markus1203/MoBiMet/Sensor_Test/Temperatur_and_Humidity/Data/FRWRTM_MET_1min_2020-04-05.csv

TOA5 | FRWRTM | CR1000X | 2600 | CR1000X.Std.03.02 | CPU:FRWRTM007.CR1X | 29908 | MET_1min
TIMESTAMP | RECORD | MET_PTB100_PressureSeaLevel_hPa_Avg | MET_PTB100_PressureActual_hPa_Avg | MET_CS215_AirTemperature_degC_Avg | MET_CS215_RelHumidity_percent_Avg | MET_CS215_DewPoint_degC_Avg | MET_CS215_VapourPressure_hPa_Avg | MET_CS215_VapPressDeficit_hPa_Avg | MET_CS215_MixingRatio_gKg_Avg | MET_CS107_SoilT05cm_degC_Avg | MET_CS107_SoilT20cm_degC_Avg
TS | RN | hPa | hPa | degC | % | degC | hPa | hPa | g/kg | degC | degC
 |  | Avg | Avg | Avg | Avg | Avg | Avg | Avg | Avg | Avg | Avg
2020-04-05 00:01:00 | 63954 | 1020.404 | 987.741 | 9.369334 | 53.05983 | 0.2502696 | 6.21867 | 5.50144 | 3.941242 | 10.80572 | 9.838089
2020-04-05 00:02:00 | 63955 | 1020.394 | 987.7316 | 9.36775 | 53.25433 | 0.2997386 | 6.240806 | 5.478066 | 3.955398 | 10.80352 | 9.836883
2020-04-05 00:03:00 | 63956 | 1020.37 | 987.7077 | 9.364333 | 52.95258 | 0.2174377 | 6.204032 | 5.512173 | 3.932038 | 10.80069 | 9.835658
2020-04-05 00:04:00 | 63957 | 1020.412 | 987.7499 | 9.370166 | 53.09183 | 0.2594223 | 6.222764 | 5.497997 | 3.943816 | 10.79503 | 9.833943
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
