markus1203/MoBiMet/Sensor_Test/Temperatur_and_Humidity/Data/FRWRTM_MET_1min_2020-04-06.csv

TOA5 | FRWRTM | CR1000X | 2600 | CR1000X.Std.03.02 | CPU:FRWRTM007.CR1X | 29908 | MET_1min
TIMESTAMP | RECORD | MET_PTB100_PressureSeaLevel_hPa_Avg | MET_PTB100_PressureActual_hPa_Avg | MET_CS215_AirTemperature_degC_Avg | MET_CS215_RelHumidity_percent_Avg | MET_CS215_DewPoint_degC_Avg | MET_CS215_VapourPressure_hPa_Avg | MET_CS215_VapPressDeficit_hPa_Avg | MET_CS215_MixingRatio_gKg_Avg | MET_CS107_SoilT05cm_degC_Avg | MET_CS107_SoilT20cm_degC_Avg
TS | RN | hPa | hPa | degC | % | degC | hPa | hPa | g/kg | degC | degC
 |  | Avg | Avg | Avg | Avg | Avg | Avg | Avg | Avg | Avg | Avg
2020-04-06 00:01:00 | 65394 | 1018.074 | 985.4112 | 9.117416 | 58.85733 | 1.465246 | 6.78321 | 4.741622 | 4.311748 | 11.76102 | 10.5164
2020-04-06 00:02:00 | 65395 | 1018.096 | 985.4339 | 9.11825 | 58.76458 | 1.443873 | 6.772895 | 4.752576 | 4.305046 | 11.75841 | 10.51471
2020-04-06 00:03:00 | 65396 | 1018.113 | 985.4507 | 9.124334 | 58.79433 | 1.456703 | 6.779078 | 4.751076 | 4.308928 | 11.75586 | 10.513
2020-04-06 00:04:00 | 65397 | 1018.112 | 985.4499 | 9.109 | 58.6995 | 1.419632 | 6.761217 | 4.757137 | 4.297502 | 11.75011 | 10.5115
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
