markus1203/MoBiMet/Sensor_Test/Temperatur_and_Humidity/Data/Ta_RH_Test-2020-04-03.csv

Time | AM2320_Ta | AM2320RH | 1_DHT22_Ta | 1_DHT22_RH | 2_DHT22_Ta | 2_DHT22_RH | 1_HTU21D_Ta | 1_HTU21D_RH | 2_HTU21D_Ta | 2_HTU21D_RH | 1_MCP9808 | 2_MCP9808 | 1_BME680_Ta | 1_BME680_RH | 1_BME680_P | 1_BME680_q | 2_BME680_Ta | 2_BME680_RH | 2_BME680_P | 2_BME680_q | 1_BME280_Ta | 1_BME280_RH | 1_BME280_P | 2_BME280_Ta | 2_BME280_RH | 2_BME280_P
2020-04-03 18:05:14 | 18.3 | 37.6 | 18.3999996185 | 28.8999996185 | 17.0 | 32.5 | 15.9990722656 | 32.1240844727 | 15.8167456055 | 32.4521484375 | 16.0625 | 16.3125 | 15.68 | 33.458 | 985.93 | 12887828 | 15.68 | 32.879 | 987.38 | 12917167 | 15.48 | 29.2887808946 | 985.581536506 | 15.24 | 15.24 | 986.07101426
2020-04-03 18:06:02 | 16.2 | 38.1 | 16.1000003815 | 31.8999996185 | 16.7999992371 | 31.8999996185 | 15.3341162109 | 35.5725708008 | 15.1839648437 | 35.6641235352 | 15.5625 | 15.875 | 15.23 | 34.886 | 985.95 | 12887828 | 15.17 | 34.578 | 987.36 | 12917167 | 15.04 | 31.5297082701 | 985.635545612 | 14.71 | 14.71 | 986.122666853
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
