markus1203/MoBiMet/Sensor_Test/Temperatur_and_Humidity/Data/Ta_RH_Test-2020-04-04.csv

Time | AM2320_Ta | AM2320RH | 1_DHT22_Ta | 1_DHT22_RH | 2_DHT22_Ta | 2_DHT22_RH | 1_HTU21D_Ta | 1_HTU21D_RH | 2_HTU21D_Ta | 2_HTU21D_RH | 1_MCP9808 | 2_MCP9808 | 1_BME680_Ta | 1_BME680_RH | 1_BME680_P | 1_BME680_q | 2_BME680_Ta | 2_BME680_RH | 2_BME680_P | 2_BME680_q | 1_BME280_Ta | 1_BME280_RH | 1_BME280_P | 2_BME280_Ta | 2_BME280_RH | 2_BME280_P
2020-04-04 00:00:04 | 6.7 | 73.7 | 6.5 | 61.7000007629 | 6.59999990463 | 64.8000030518 | 6.23923339844 | 65.0983276367 | 5.96038085938 | 65.5255737305 | 6.5625 | 6.375 | 6.38 | 61.486 | 989.18 | 12887828 | 6.53 | 60.228 | 990.81 | 12917167 | 5.55 | 60.5524837484 | 988.842023691 | 5.74 | 5.74 | 989.306324585
2020-04-04 00:01:01 | 6.7 | 73.9 | 6.5 | 61.7000007629 | 6.69999980927 | 64.3000030518 | 6.22850830078 | 65.1517333984 | 5.96038085938 | 65.5942382812 | 6.5625 | 6.375 | 6.38 | 61.541 | 989.13 | 12887828 | 6.53 | 60.28 | 990.8 | 12917167 | 5.53 | 60.7136081599 | 988.773499266 | 5.73 | 5.73 | 989.316546032
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
