markus1203/MoBiMet/Sensor_Test/Temperatur_and_Humidity/Humidity/1_BME680_VPvsCS215.png

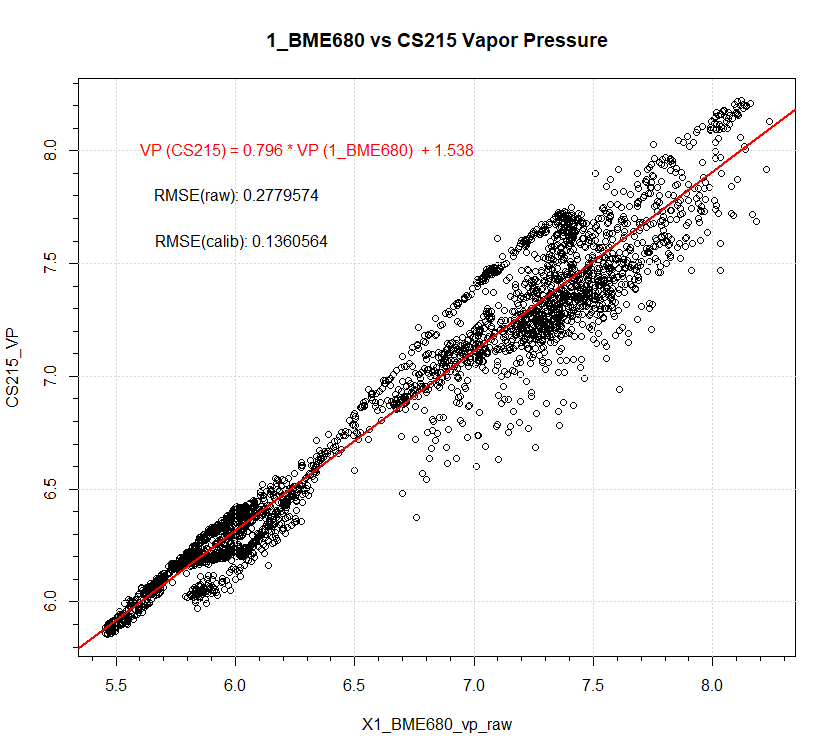
Sensor_Test/Temperatur_and_Humidity/Humidity/1_BME680_VPvsCS215.png
