markus1203/MoBiMet/Sensor_Test/Temperatur_and_Humidity/Humidity/1_HTU21DvsCS215.png

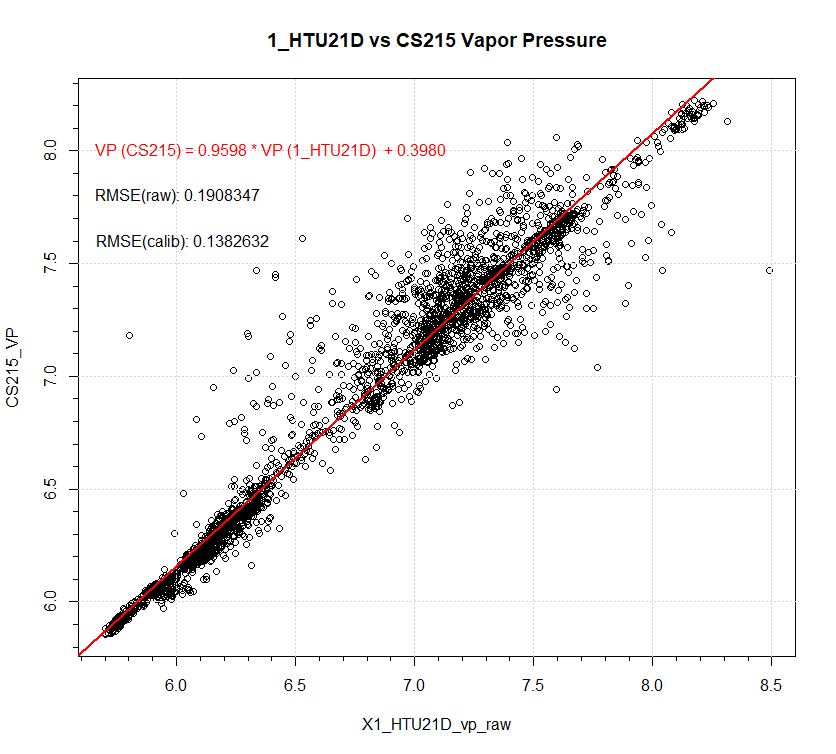
Sensor_Test/Temperatur_and_Humidity/Humidity/1_HTU21DvsCS215.png
