markus1203/MoBiMet/Sensor_Test/Temperatur_and_Humidity/Humidity/2_DHT22_RHvsTIME.png

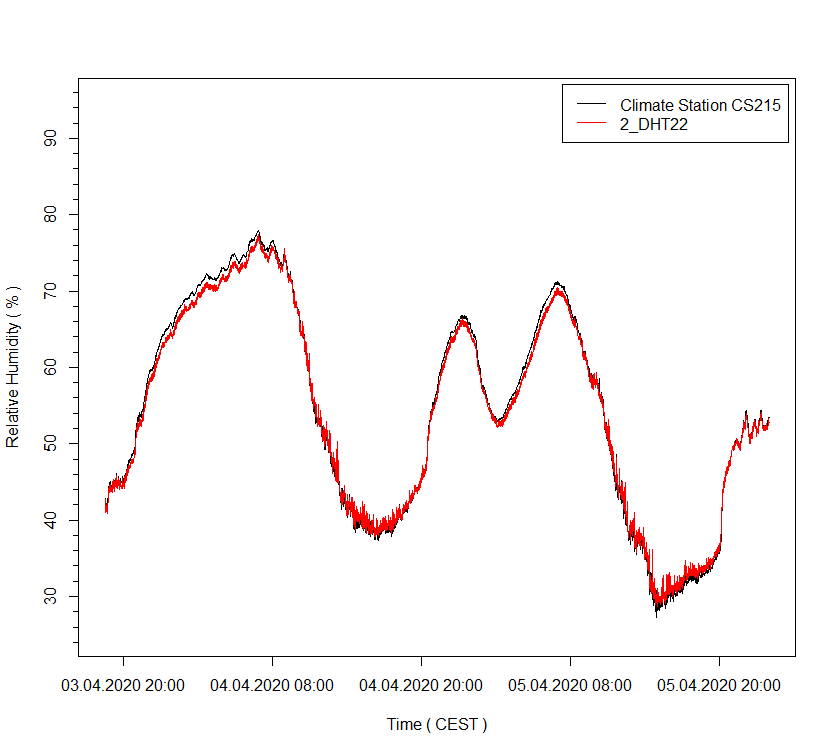
Sensor_Test/Temperatur_and_Humidity/Humidity/2_DHT22_RHvsTIME.png
