markus1203/MoBiMet/Sensor_Test/Temperatur_and_Humidity/Humidity/2_HTU21D_VPvsCS215.png

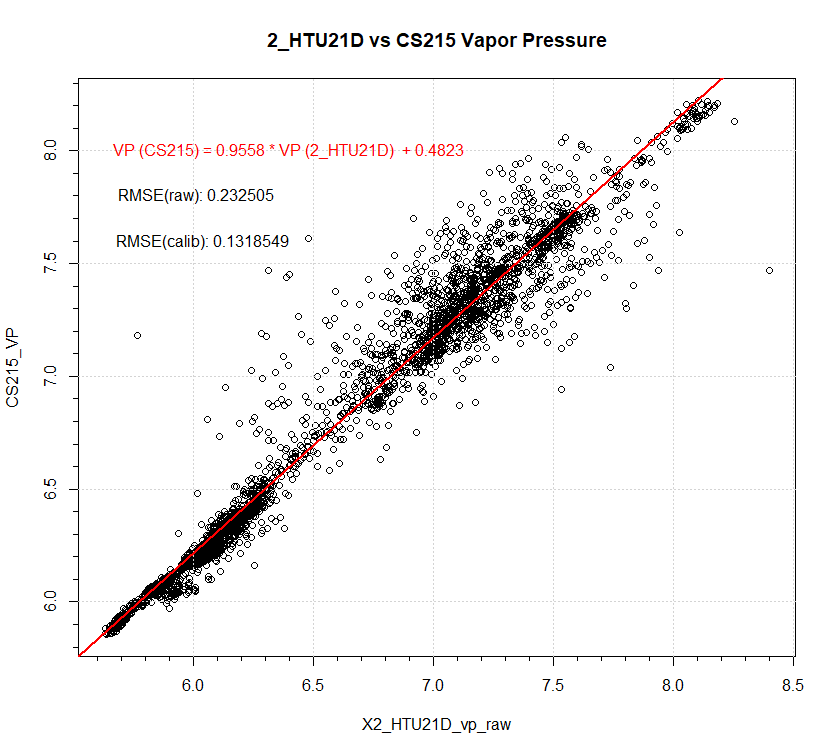
Sensor_Test/Temperatur_and_Humidity/Humidity/2_HTU21D_VPvsCS215.png
