markus1203/MoBiMet/Sensor_Test/Temperatur_and_Humidity/Humidity/AM2320_RHvsTIME.png

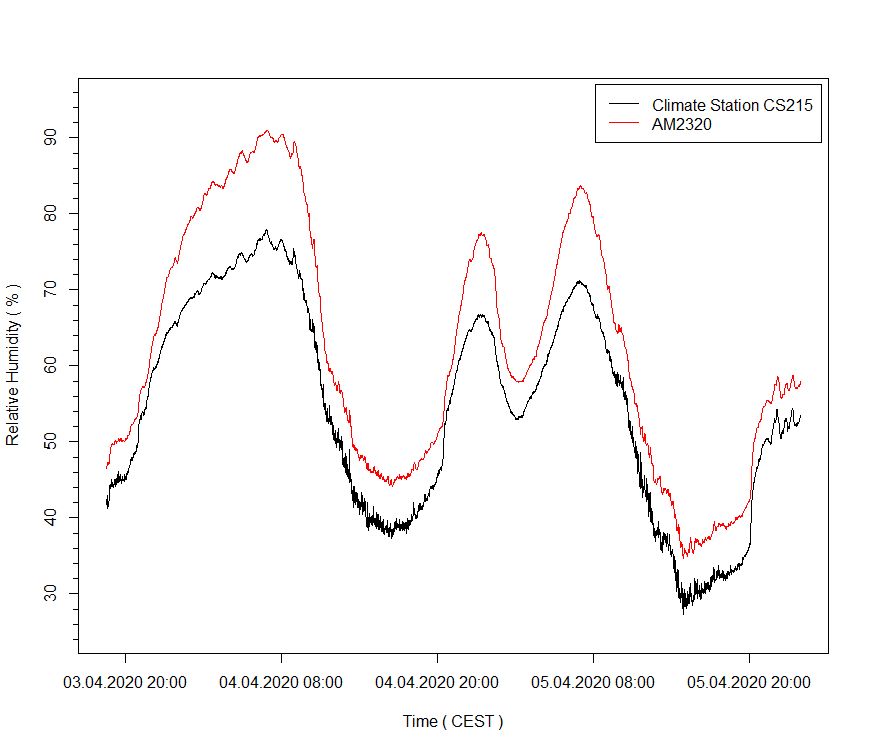
Sensor_Test/Temperatur_and_Humidity/Humidity/AM2320_RHvsTIME.png
