markus1203/MoBiMet/Sensor_Test/Temperatur_and_Humidity/Humidity/RH_all.png

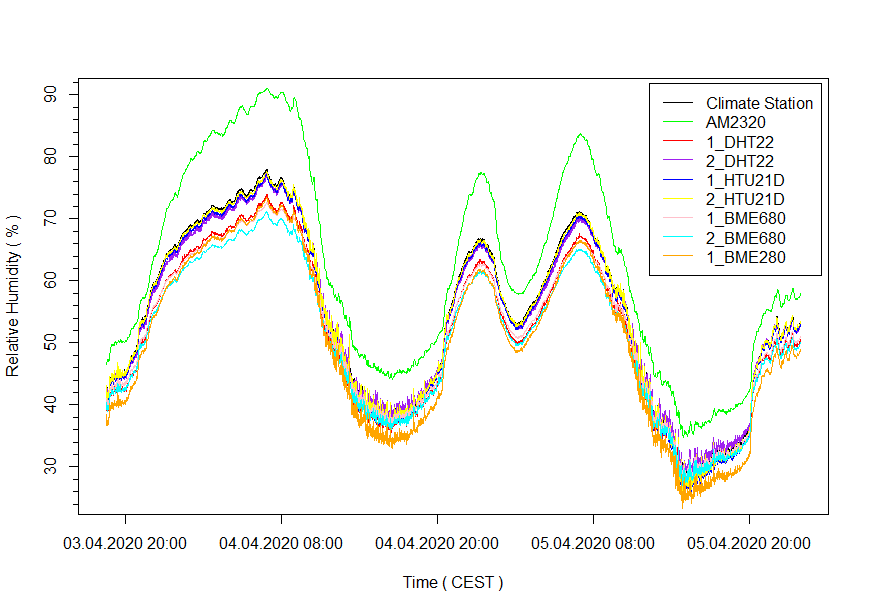
Sensor_Test/Temperatur_and_Humidity/Humidity/RH_all.png
