markus1203/MoBiMet/Sensor_Test/Temperatur_and_Humidity/Humidity/VP_all.png

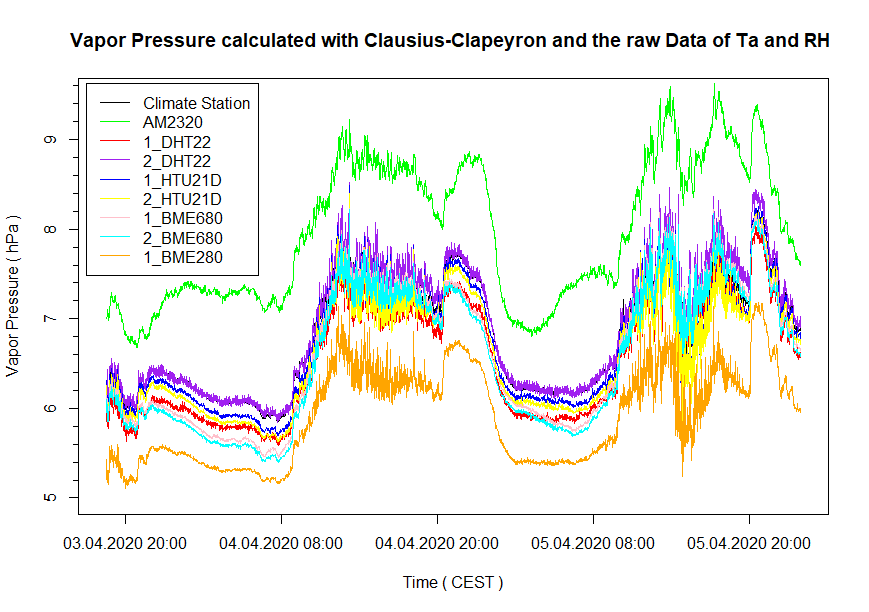
Sensor_Test/Temperatur_and_Humidity/Humidity/VP_all.png
