markus1203/MoBiMet/Sensor_Test/Temperatur_and_Humidity/Pressure/1_BME280_PvsTIME.png

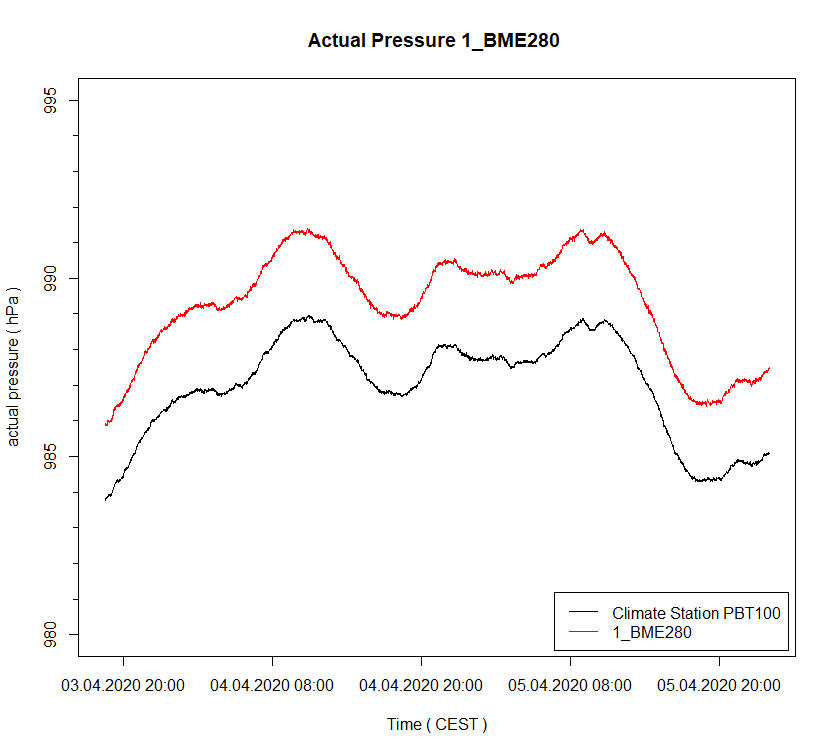
Sensor_Test/Temperatur_and_Humidity/Pressure/1_BME280_PvsTIME.png
