markus1203/MoBiMet/Sensor_Test/Temperatur_and_Humidity/Pressure/2_BME680_PvsTIME.png

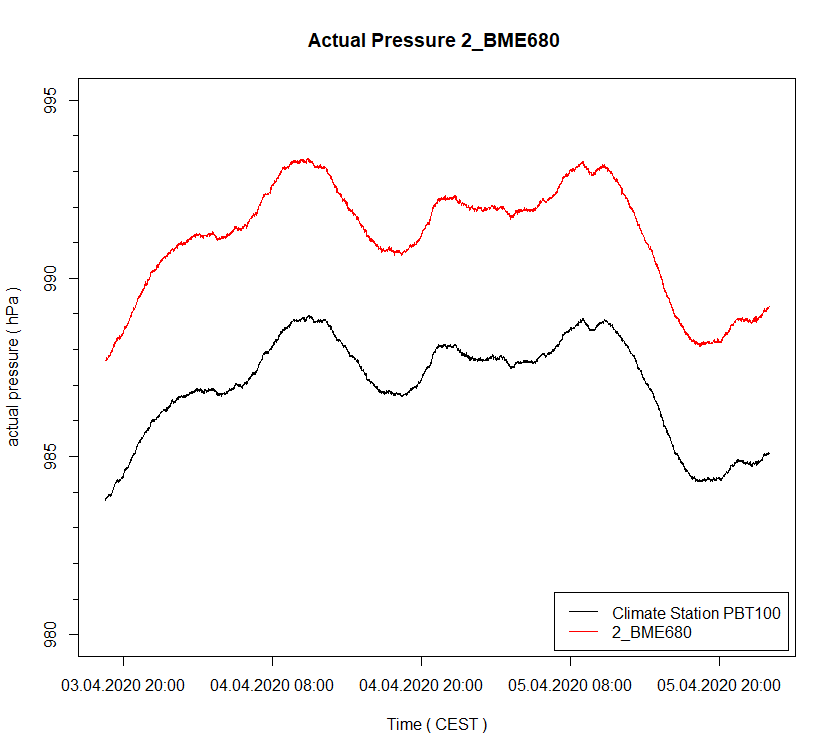
Sensor_Test/Temperatur_and_Humidity/Pressure/2_BME680_PvsTIME.png
