markus1203/MoBiMet/Sensor_Test/Temperatur_and_Humidity/Ta/1_BME280vsTIME.png

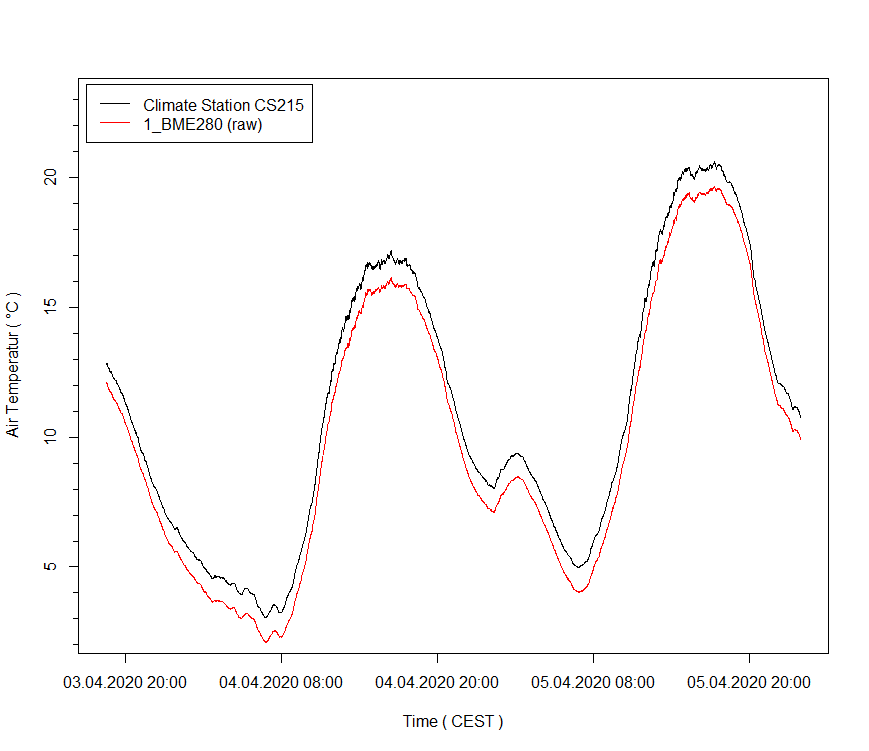
Sensor_Test/Temperatur_and_Humidity/Ta/1_BME280vsTIME.png
