markus1203/MoBiMet/Sensor_Test/Temperatur_and_Humidity/Ta/1_MCP9808vsCS215.png

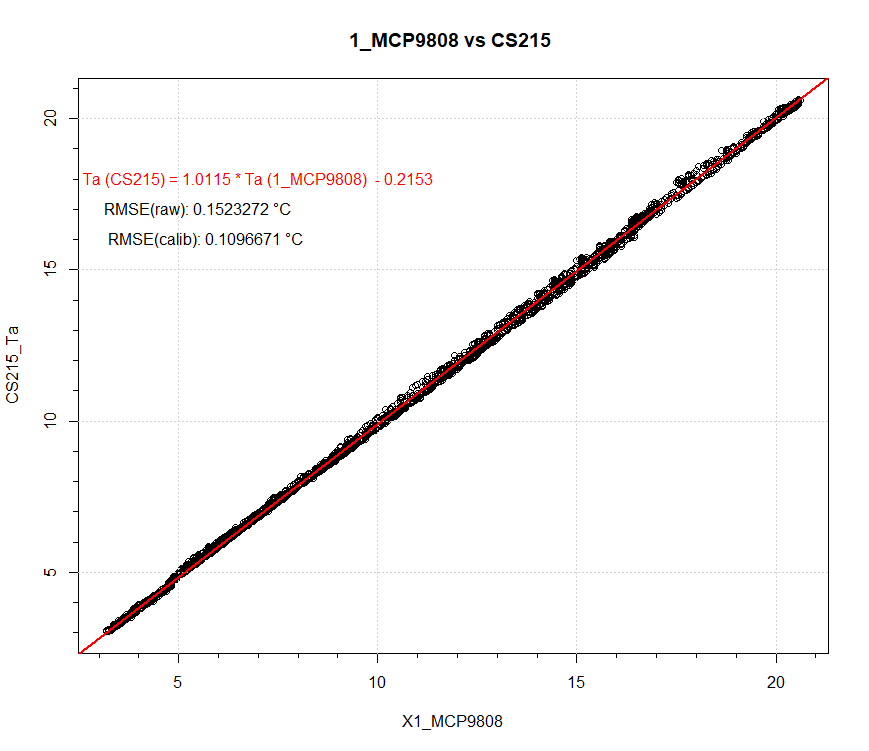
Sensor_Test/Temperatur_and_Humidity/Ta/1_MCP9808vsCS215.png
