markus1203/MoBiMet/Sensor_Test/Temperatur_and_Humidity/Ta/Ta_all.png

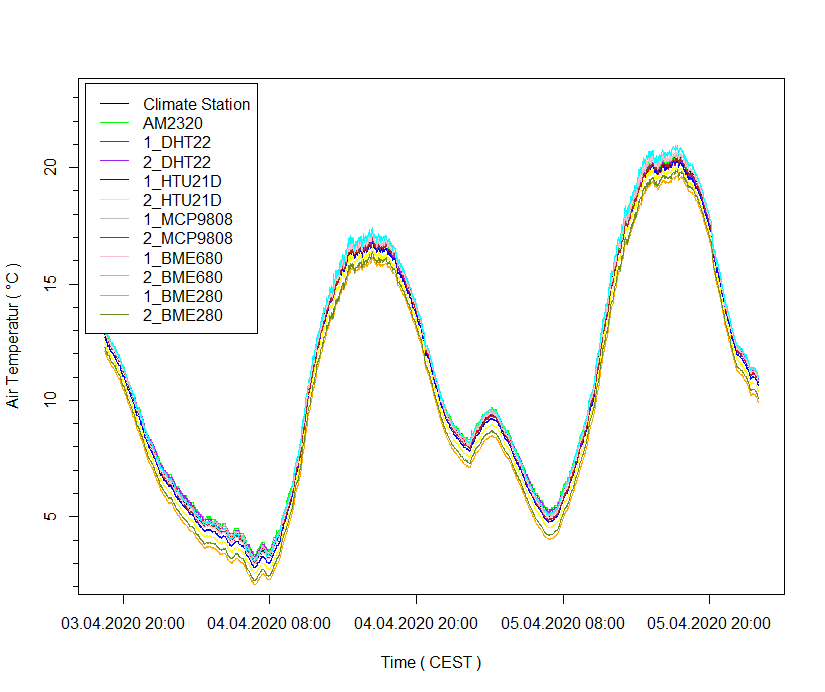
Sensor_Test/Temperatur_and_Humidity/Ta/Ta_all.png
